maduwanthasl/Golem-SLRC-2024/3d printed parts/mg995-16.snapshot.2/Braket_mg995_2.SLDPRT

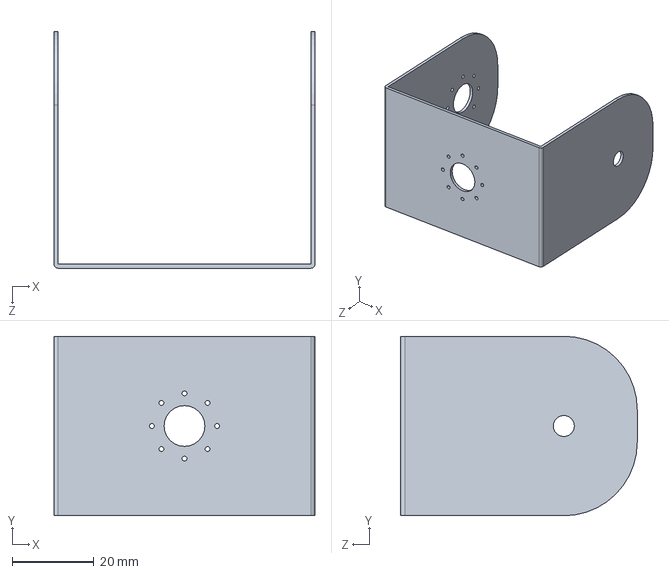
[picture p16: CAD file, 2024-05-11]
3d printed parts/mg995-16.snapshot.2/Braket_mg995_2.SLDPRT
64.0 x 44.0 x 58.0 mm
