maduwanthasl/Golem-SLRC-2024/3d printed parts/mg995-servo-motor-metal-horn-1.snapshot.2/servo horn.step

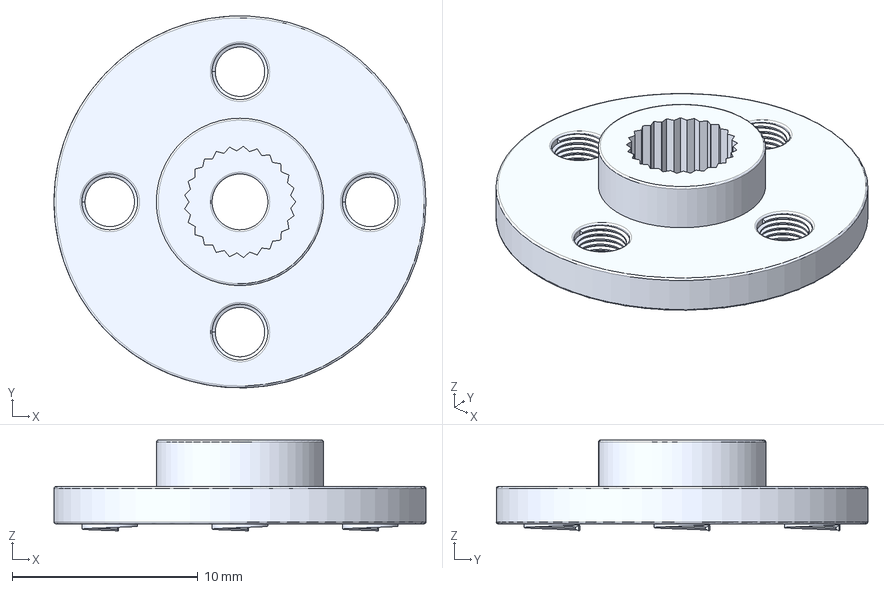
[picture p17: CAD file, 2024-05-11]
3d printed parts/mg995-servo-motor-metal-horn-1.snapshot.2/servo horn.step
20.0 x 20.0 x 4.88 mm
