maduwanthasl/Golem-SLRC-2024/3d printed parts/mounting-hub-at-torque-side-for-rds3115-servo-1.snapshot.1/Hub_torque.stp

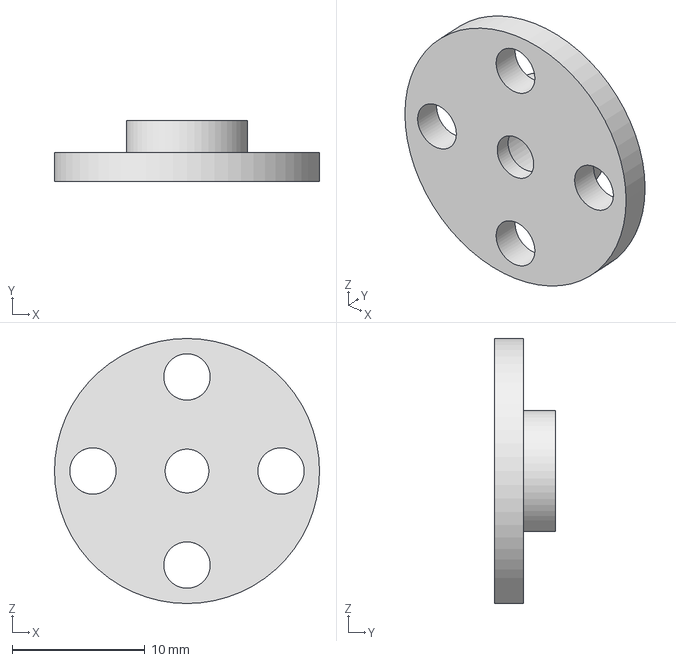
[picture p18: CAD file, 2024-05-11]
3d printed parts/mounting-hub-at-torque-side-for-rds3115-servo-1.snapshot.1/Hub_torque.stp
20.0 x 4.60 x 20.0 mm
