maduwanthasl/Golem-SLRC-2024/3d printed parts/Tof_sensor_holder.SLDPRT

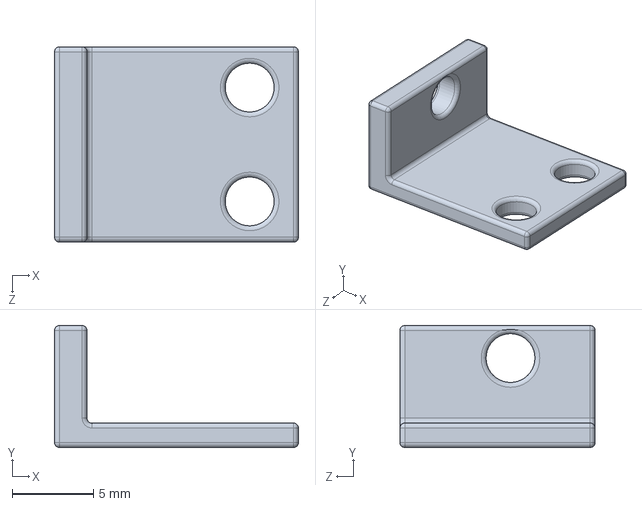
[picture p19: CAD file, 2024-05-11]
3d printed parts/Tof_sensor_holder.SLDPRT
15.0 x 7.50 x 12.0 mm
