maduwanthasl/Golem-SLRC-2024/3d printed parts/mg995-16.snapshot.2/m995.SLDPRT

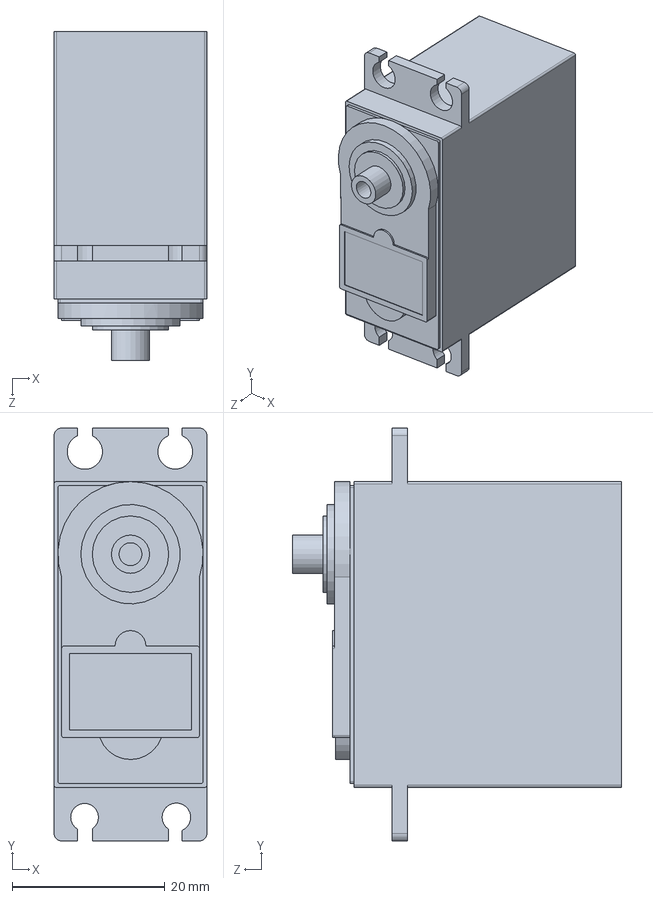
[picture p20: CAD file, 2024-05-11]
3d printed parts/mg995-16.snapshot.2/m995.SLDPRT
20.0 x 54.0 x 43.0 mm
