maduwanthasl/Golem-SLRC-2024/3d printed parts/Arm handle large.SLDPRT

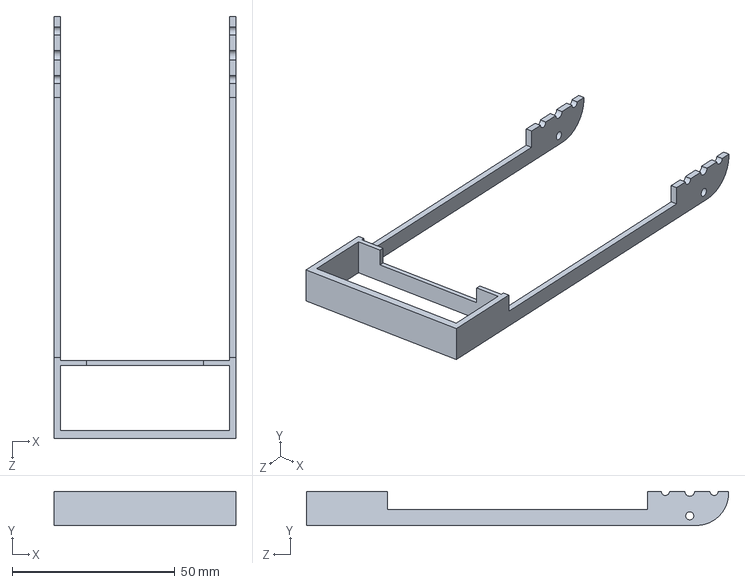
[picture p21: CAD file, 2024-05-11]
3d printed parts/Arm handle large.SLDPRT
56.0 x 10.5 x 130.0 mm
