maduwanthasl/Golem-SLRC-2024/3d printed parts/mg995-16.snapshot.2/Braket_mg995.SLDPRT

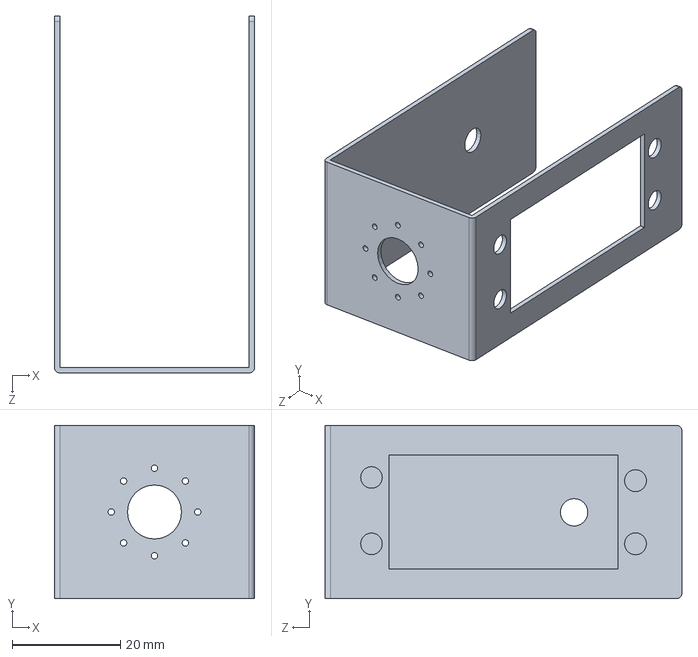
[picture p22: CAD file, 2024-05-11]
3d printed parts/mg995-16.snapshot.2/Braket_mg995.SLDPRT
37.0 x 32.0 x 66.0 mm
