maduwanthasl/Golem-SLRC-2024/3d printed parts/robot-claw-robot-gripper-gripper-manipulator-mechanical-claw-arm-1.snapshot.3/kiskac1.SLDPRT

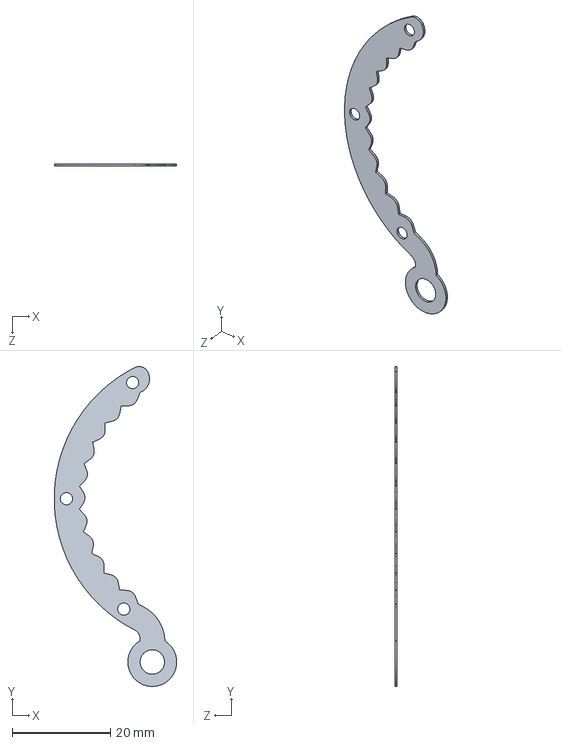
[picture p23: CAD file, 2024-05-11]
3d printed parts/robot-claw-robot-gripper-gripper-manipulator-mechanical-claw-arm-1.snapshot.3/kiskac1.SLDPRT
25.0 x 65.2 x 0.5 mm
