maduwanthasl/Golem-SLRC-2024/3d printed parts/servo mini holder.STL

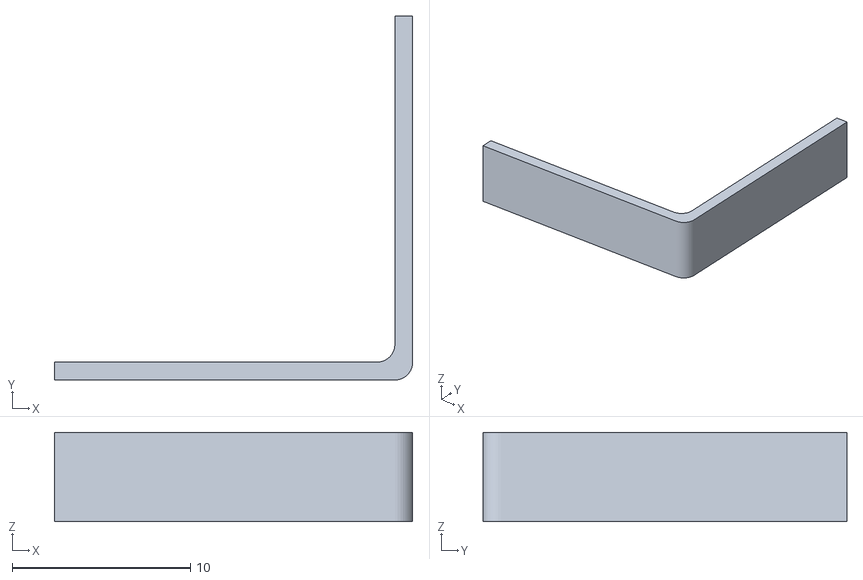
[picture p24: CAD file, 2024-05-11]
3d printed parts/servo mini holder.STL
20.1 x 20.4 x 5.00
