maduwanthasl/Golem-SLRC-2024/3d printed parts/servo hub large.STL

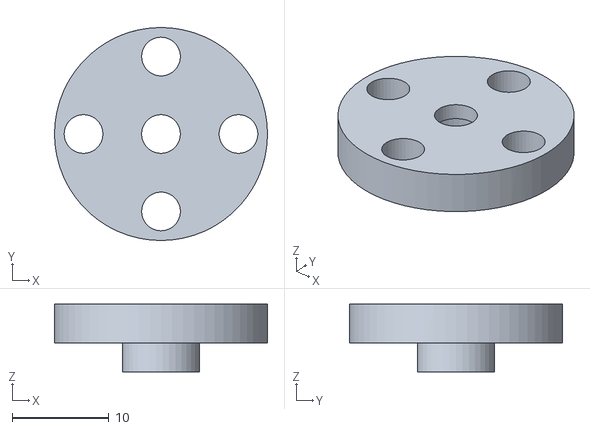
[picture p25: CAD file, 2024-05-11]
3d printed parts/servo hub large.STL
22.0 x 22.0 x 7.00
