maduwanthasl/Golem-SLRC-2024/3d printed parts/Arm handle.SLDPRT

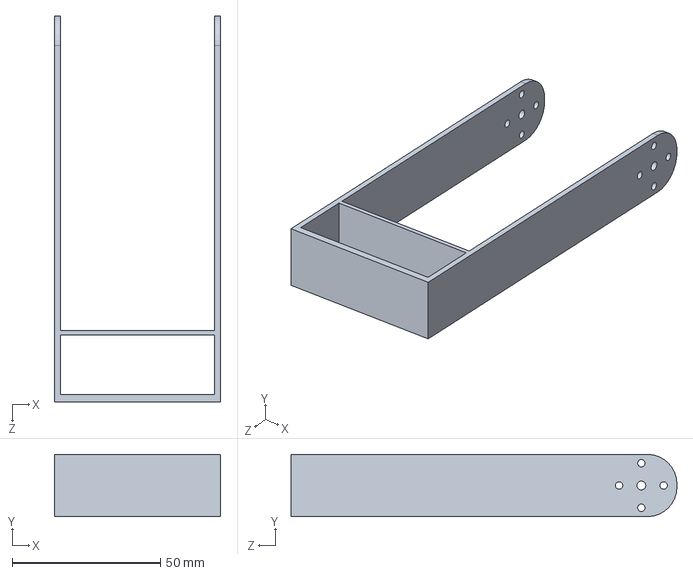
[picture p26: CAD file, 2024-05-11]
3d printed parts/Arm handle.SLDPRT
56.0 x 21.0 x 130.0 mm
