maduwanthasl/Golem-SLRC-2024/3d printed parts/robot-claw-robot-gripper-gripper-manipulator-mechanical-claw-arm-1.snapshot.3/araparca.SLDPRT

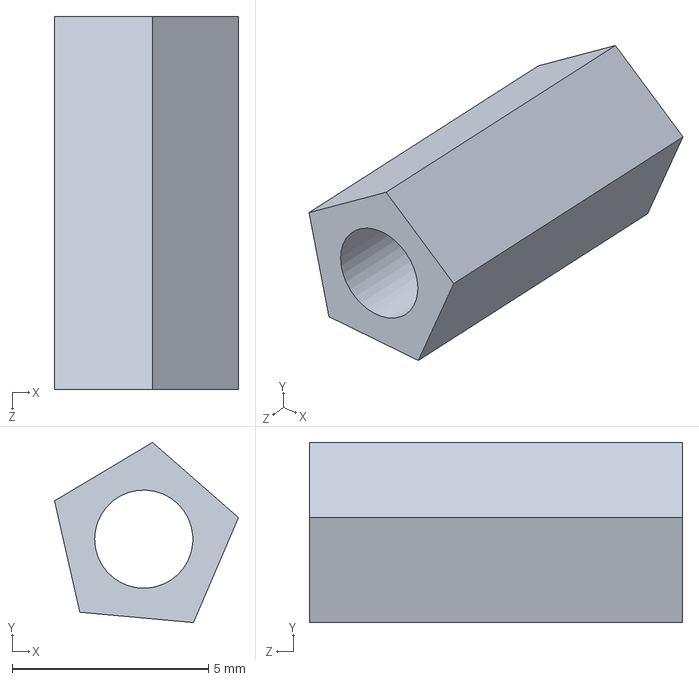
[picture p27: CAD file, 2024-05-11]
3d printed parts/robot-claw-robot-gripper-gripper-manipulator-mechanical-claw-arm-1.snapshot.3/araparca.SLDPRT
4.68 x 4.59 x 9.50 mm
