maduwanthasl/Golem-SLRC-2024/3d printed parts/LCD Display Holder.SLDPRT

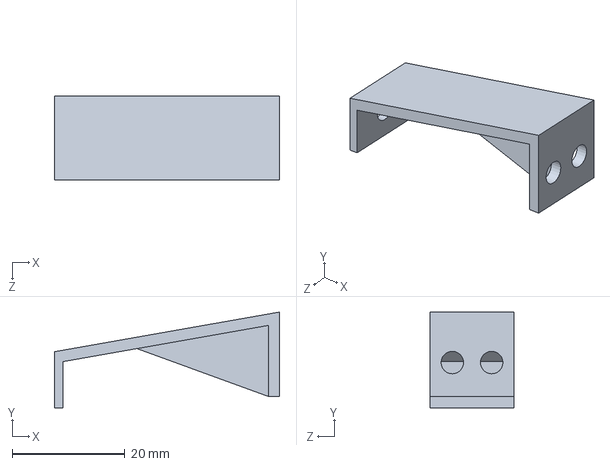
[picture p28: CAD file, 2024-05-11]
3d printed parts/LCD Display Holder.SLDPRT
40.0 x 17.1 x 15.0 mm
