maduwanthasl/Golem-SLRC-2024/3d printed parts/servohub.STL

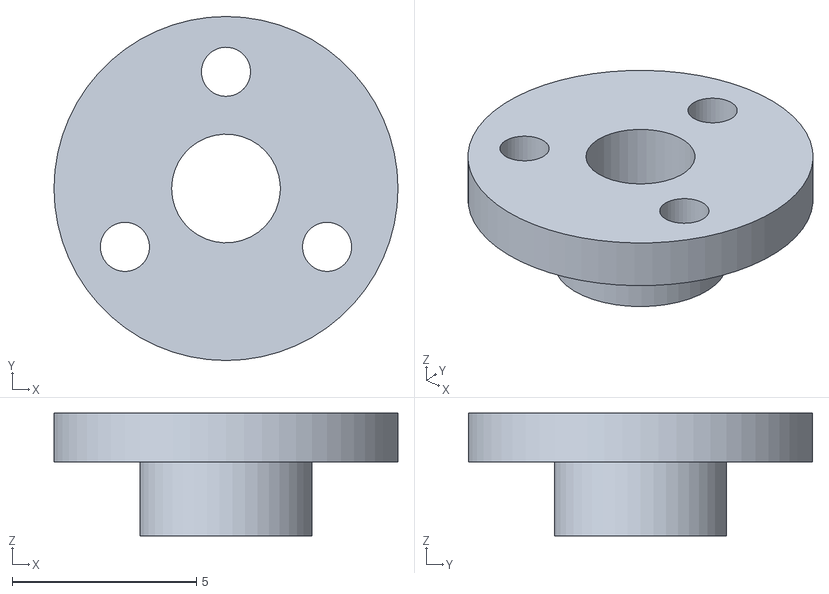
[picture p29: CAD file, 2024-05-11]
3d printed parts/servohub.STL
9.33 x 9.33 x 3.33
