maduwanthasl/Golem-SLRC-2024/3d printed parts/ultrasonic_holder.SLDPRT

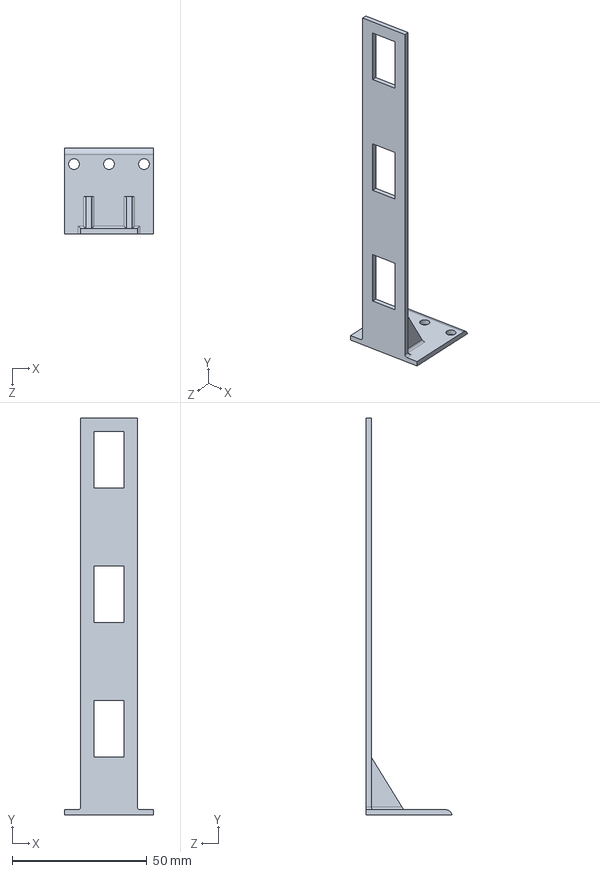
[picture p30: CAD file, 2024-05-11]
3d printed parts/ultrasonic_holder.SLDPRT
33.0 x 147.5 x 32.0 mm
