maduwanthasl/Golem-SLRC-2024/3d printed parts/serrvoArm_holde.SLDPRT

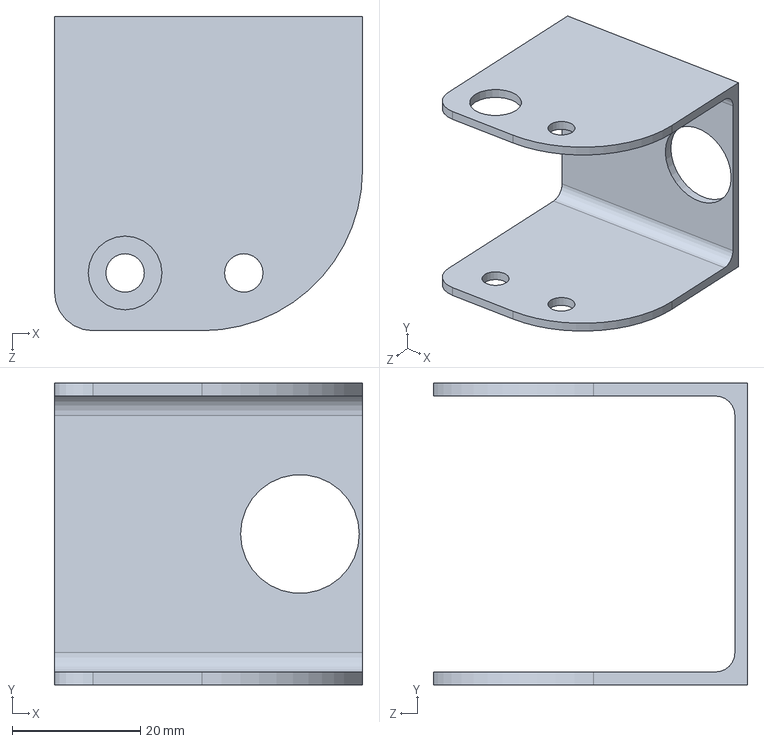
[picture p31: CAD file, 2024-05-11]
3d printed parts/serrvoArm_holde.SLDPRT
48.0 x 47.0 x 49.0 mm
