maduwanthasl/Golem-SLRC-2024/3d printed parts/handle 3-need 8.STL

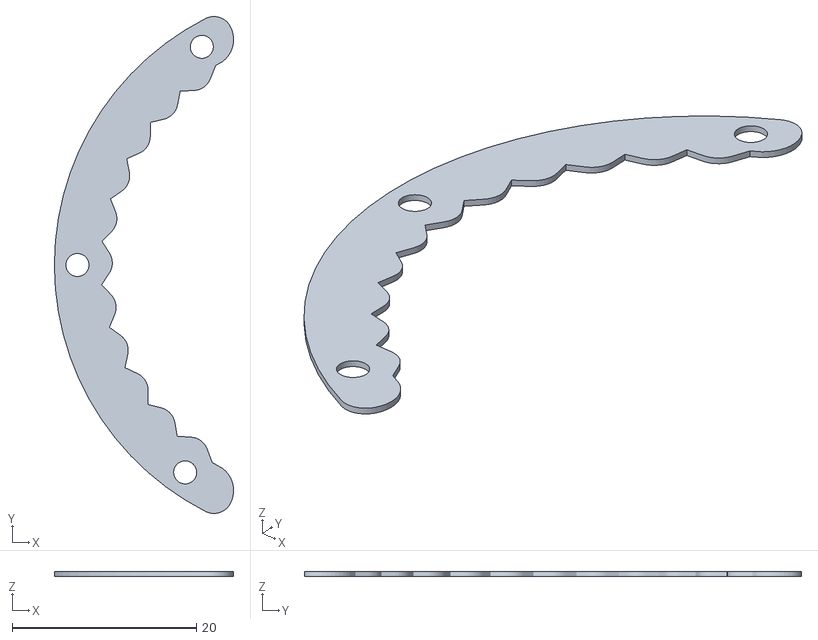
[picture p32: CAD file, 2024-05-11]
3d printed parts/handle 3-need 8.STL
19.4 x 53.9 x 0.5
