maduwanthasl/Golem-SLRC-2024/3d printed parts/Servo holder.SLDPRT

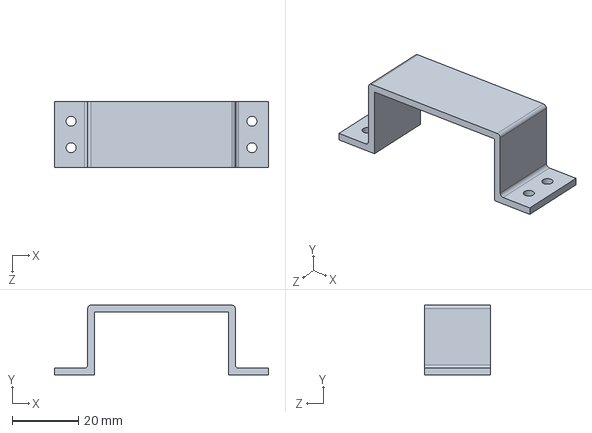
[picture p33: CAD file, 2024-05-11]
3d printed parts/Servo holder.SLDPRT
64.5 x 21.0 x 20.0 mm
