maduwanthasl/Golem-SLRC-2024/3d printed parts/plate.STL

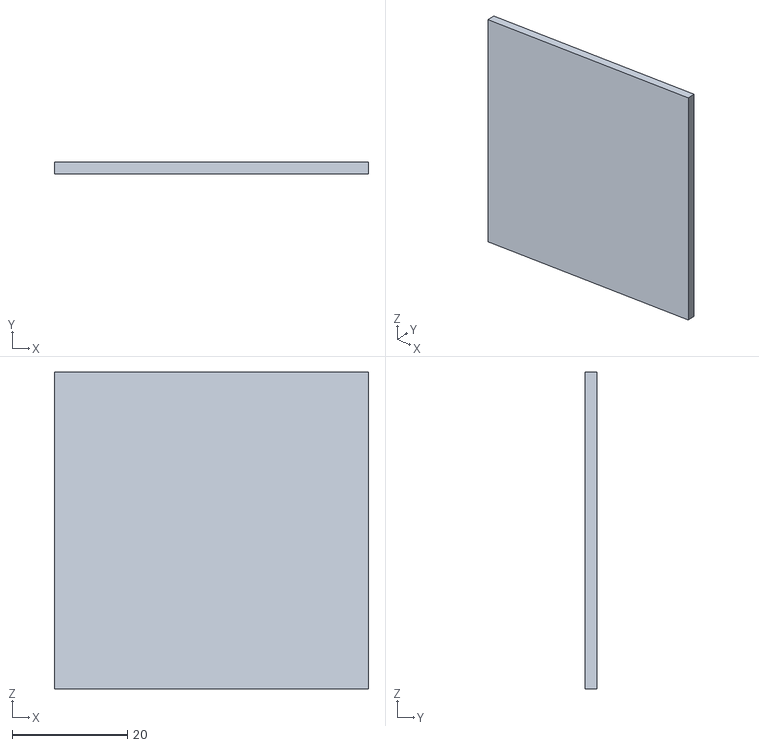
[picture p34: CAD file, 2024-05-11]
3d printed parts/plate.STL
54.5 x 2.00 x 55.0
