maduwanthasl/Golem-SLRC-2024/3d printed parts/motor_mount_2.STL

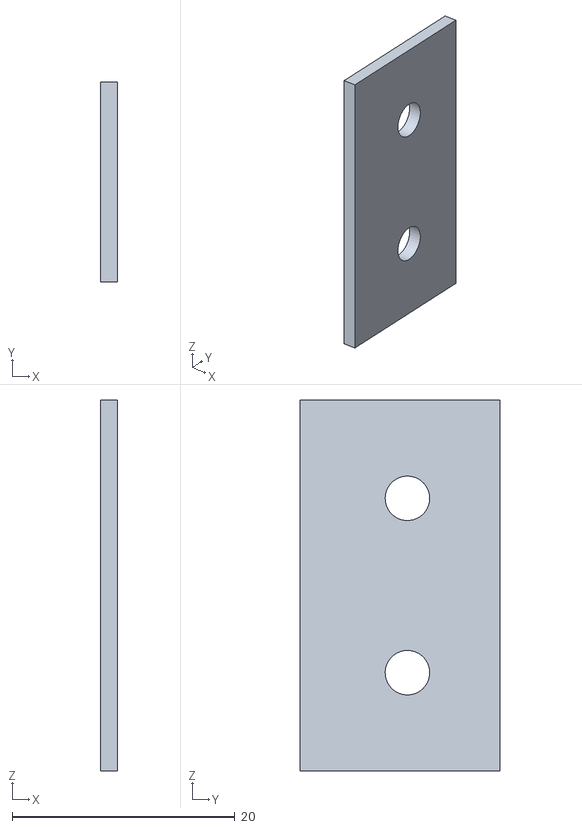
[picture p35: CAD file, 2024-05-11]
3d printed parts/motor_mount_2.STL
1.50 x 18.0 x 33.3
