maduwanthasl/Golem-SLRC-2024/3d printed parts/Reverse Ir array.SLDPRT

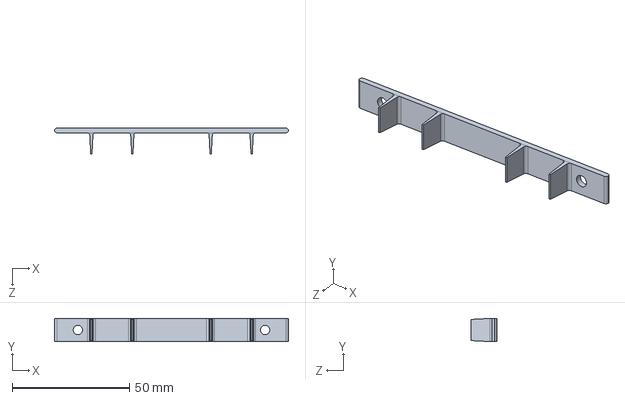
[picture p36: CAD file, 2024-05-11]
3d printed parts/Reverse Ir array.SLDPRT
100.0 x 10.0 x 11.0 mm
