maduwanthasl/Golem-SLRC-2024/3d printed parts/motor_mount.STL

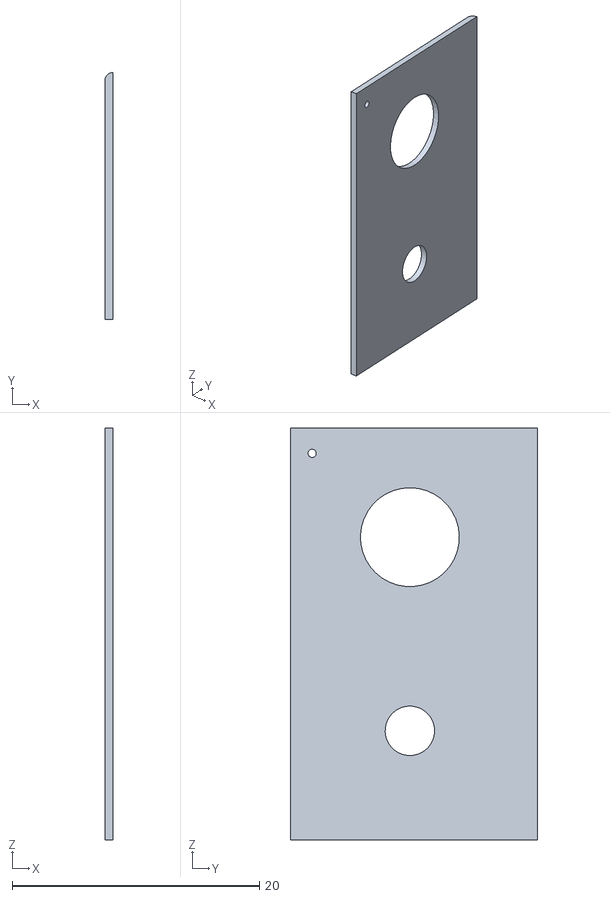
[picture p37: CAD file, 2024-05-11]
3d printed parts/motor_mount.STL
0.667 x 20.0 x 33.3
