maduwanthasl/Golem-SLRC-2024/3d printed parts/U-sac.STL

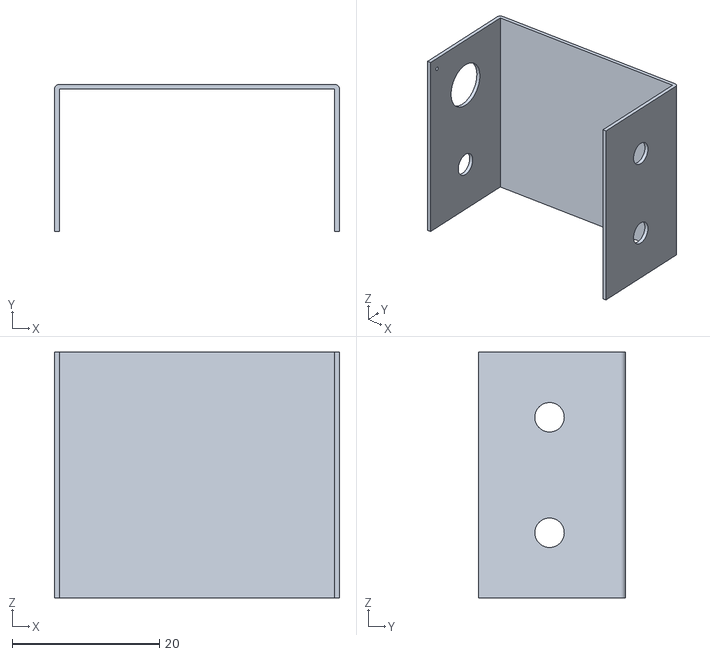
[picture p38: CAD file, 2024-05-11]
3d printed parts/U-sac.STL
38.7 x 20.0 x 33.3
