maduwanthasl/Golem-SLRC-2024/3d printed parts/LCD Display.SLDPRT

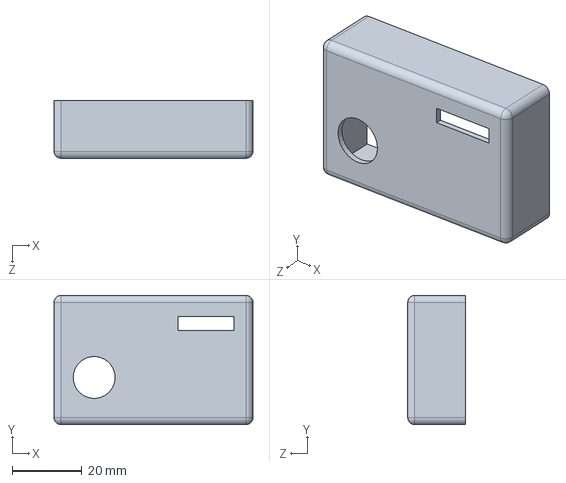
[picture p39: CAD file, 2024-05-11]
3d printed parts/LCD Display.SLDPRT
57.0 x 37.0 x 16.5 mm
