maduwanthasl/Golem-SLRC-2024/two_encoder_motors/two_encoder_motors.ino

#include <util/atomic.h>

// A class to compute the control signal
class SimplePID{
  private:
    float kp, kd, ki, umax; // Parameters
    float eprev, eintegral; // Storage

  public:
  // Constructor
  SimplePID() : kp(1), kd(0), ki(0), umax(255), eprev(0.0), eintegral(0.0){}

  // A function to set the parameters
  void setParams(float kpIn, float kdIn, float kiIn, float umaxIn){
    kp = kpIn; kd = kdIn; ki = kiIn; umax = umaxIn;
  }

  // A function to compute the control signal
  void evalu(int value, int target, float deltaT, int &pwr, int &dir){
    // error
    int e = target - value;
  
    // derivative
    float dedt = (e-eprev)/(deltaT);
  
    // integral
    eintegral = eintegral + e*deltaT;
  
    // control signal
    float u = kp*e + kd*dedt + ki*eintegral;
  
    // motor power
    pwr = (int) fabs(u);
    if( pwr > umax ){
      pwr = umax;
    }
  
    // motor direction
    dir = 1;
    if(u<0){
      dir = -1;
    }
  
    // store previous error
    eprev = e;
  }
  
};

// How many motors
#define NMOTORS 2

// Pins
const int enca[] = {3,19};
const int encb[] = {2,18};
const int pwm[] = {9,8};
const int in1[] = {26,22};
const int in2[] = {28,24};

// Globals
long prevT = 0;
volatile int posi[] = {0,0};

// PID class instances
SimplePID pid[NMOTORS];

void setup() {
  Serial.begin(9600);

  for(int k = 0; k < NMOTORS; k++){
    pinMode(enca[k],INPUT);
    pinMode(encb[k],INPUT);
    pinMode(pwm[k],OUTPUT);
    pinMode(in1[k],OUTPUT);
    pinMode(in2[k],OUTPUT);

    pid[k].setParams(1,0,0,255);
  }
  
  attachInterrupt(digitalPinToInterrupt(enca[0]),readEncoder<0>,RISING);
  attachInterrupt(digitalPinToInterrupt(enca[1]),readEncoder<1>,RISING);
  
  Serial.println("target pos");
}
void loop() {
  // Set target position
  int target[NMOTORS];
  // Increase the current position by 2000 counts for forward rotation
  target[0] =  2000;
  target[1] = 2000;

  // Time difference
  long currT = micros();
  float deltaT = ((float)(currT - prevT)) / (1.0e6);
  prevT = currT;

  // Read the position in an atomic block to avoid a potential misread
  int pos[NMOTORS];
  ATOMIC_BLOCK(ATOMIC_RESTORESTATE) {
    for (int k = 0; k < NMOTORS; k++) {
      pos[k] = posi[k];
    }
  }

  // Loop through the motors
  for (int k = 0; k < NMOTORS; k++) {
    int pwr, dir;
    // Evaluate the control signal
    pid[k].evalu(pos[k], target[k], deltaT, pwr, dir);
    // Signal the motor
    setMotor(dir, pwr, pwm[k], in1[k], in2[k]);
  }

  for (int k = 0; k < NMOTORS; k++) {
    Serial.print(target[k]);
    Serial.print(" ");
    Serial.print(pos[k]);
    Serial.print(" ");
  }
  Serial.println();
}


void setMotor(int dir, int pwmVal, int pwm, int in1, int in2){
  analogWrite(pwm,pwmVal);
  if(dir == 1){
    digitalWrite(in1,HIGH);
    digitalWrite(in2,LOW);
  }
  else if(dir == -1){
    digitalWrite(in1,LOW);
    digitalWrite(in2,HIGH);
  }
  else{
    digitalWrite(in1,LOW);
    digitalWrite(in2,LOW);
  }  
}

template <int j>
void readEncoder(){
  int b = digitalRead(encb[j]);
  if(b > 0){
    posi[j]++;
  }
  else{
    posi[j]--;
  }
}
