maduwanthasl/Golem-SLRC-2024/PID_line_follow_controling_in_display/motor_drive.h

#ifndef MOTOR_DRIVE_H
#define MOTOR_DRIVE_H
#include <Arduino.h>
#include "pins.h"


void forward();
void reverse();
void left();
void right();
void sharpLeftTurn();
void sharpRightTurn();
void stop_bot();



#endif
