maduwanthasl/Golem-SLRC-2024/PID_line_follow_controling_in_display/motor_pwm_control.h

#ifndef MOTOR_PWM_CONTROL_H
#define MOTOR_PWM_CONTROL_H
#include <Arduino.h>
#include "pins.h"
#include "variables.h"
#include "calculate_pid.h"
#include "motor_drive.h"

void motor_control();

#endif
