maduwanthasl/Golem-SLRC-2024/PID_line_follow_controling_v8_calibration_reverse/color_sensor.h

/*
code1

#ifndef COLOR_SENSOR_H
#define COLOR_SENSOR_H

#include <Wire.h>
#include "Adafruit_TCS34725.h"

extern int redCount;
extern int greenCount;
extern int blueCount;

extern unsigned long startTime;

void setup_color_sensor();
void loop_color_sensor();

#endif

code 2

*/

#ifndef COLOR_SENSOR_H
#define COLOR_SENSOR_H

#include <Wire.h>
#include "Adafruit_TCS34725.h"
#include "variables.h"

class ColorSensor {
public:
    ColorSensor();
    void setup();
    void loop();

private:
    Adafruit_TCS34725 tcs;
    int redCount;
    int greenCount;
    int blueCount;
    
};

#endif

/*


#ifndef COLOR_SENSOR_H
#define COLOR_SENSOR_H

#include <Arduino.h>
#include "variables.h"

#define S0 38
#define S1 40
#define S2 42
#define S3 44
#define sensorOut 46

class ColorSensor {
  public:
    ColorSensor();
    void setup();
    void loop();

  private:
    int redFrequency;
    int greenFrequency;
    int blueFrequency;
};

#endif

*/
