maduwanthasl/Golem-SLRC-2024/PID_line_follow_controling_v8_calibration_reverse/measure_distance_tof.h

#ifndef MEASURE_DISTANCE_TOF_H
#define MEASURE_DISTANCE_TOF_H

#include <Arduino.h>
#include "line_follow.h"
#include "Adafruit_VL53L0X.h"
#include "measure_distance_tof.h"

void measure_distance_tof_setup();
void measure_distance_tof_loop(int numSamples);


#endif
